MakersAsylumIndia/IS2026_Team02_Optical_Morse/Electronics/circuit_image.png

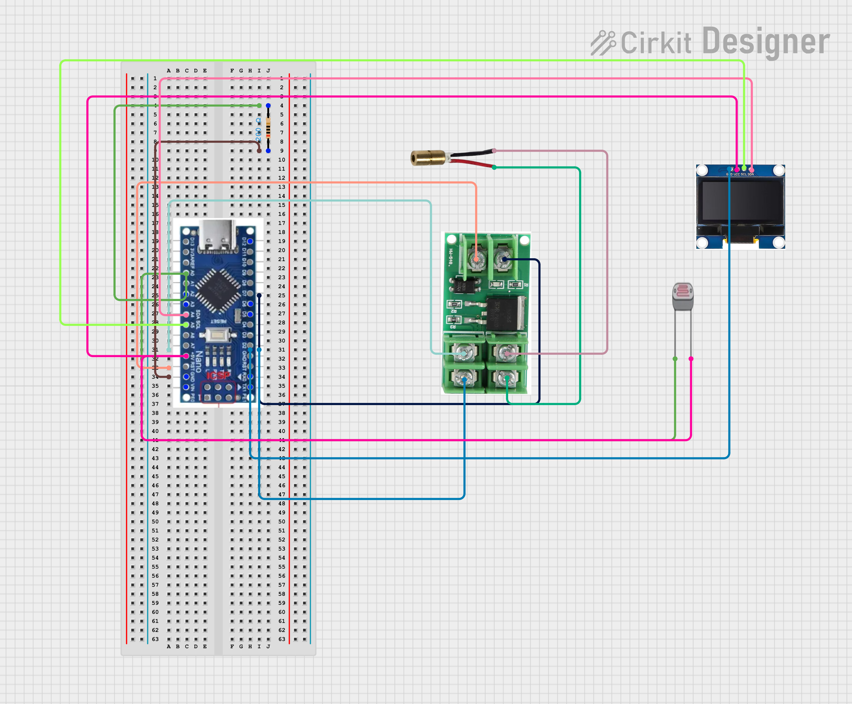
Electronics/circuit_image.png
