MakersAsylumIndia/IS2026_Team02_Optical_Morse/Photos_Videos/Images/IS2026_Team02_Optical_Morse_photo_26.jpg

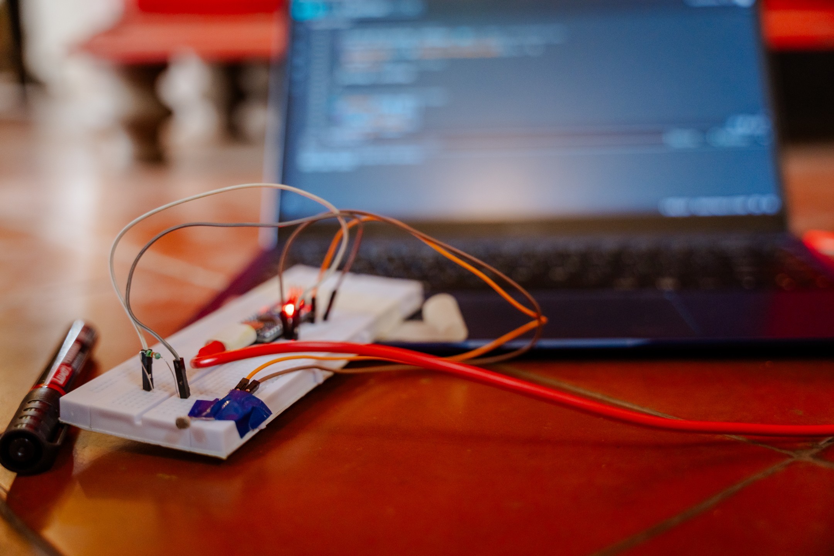
Photos_Videos/Images/IS2026_Team02_Optical_Morse_photo_26.jpg
